ri-scythe/Wild-air-quality-monitor/Firmware/Display/Untitled27_20260325142343.png

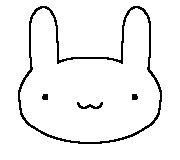
Firmware/Display/Untitled27_20260325142343.png
